m-gracia/esp32-bike-computer-main/docs/LCD_Round01.png

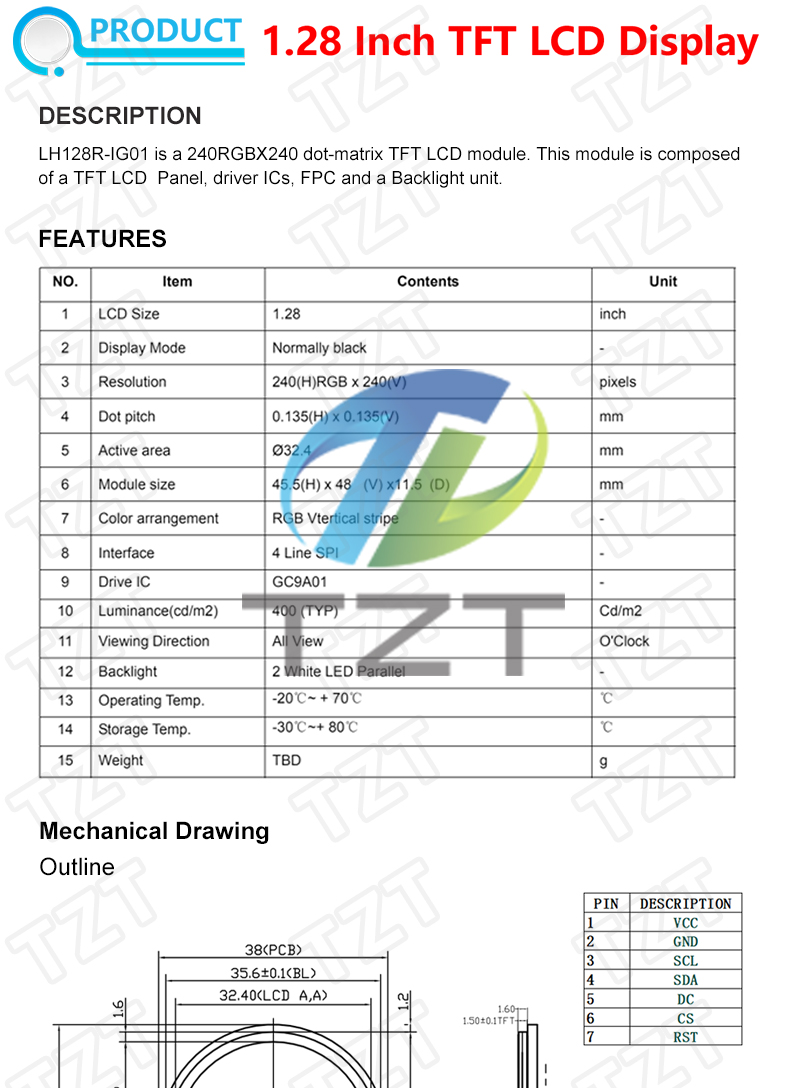
docs/LCD_Round01.png
