m-gracia/esp32-bike-computer-main/docs/LCD_Round02.png

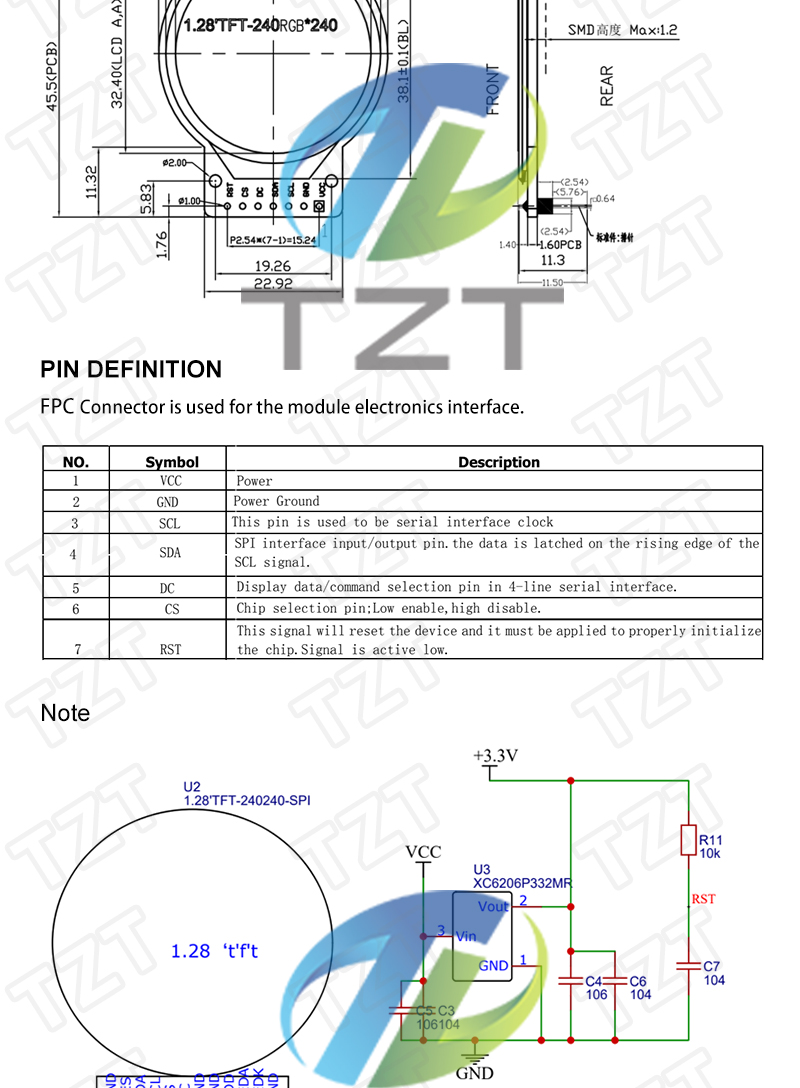
docs/LCD_Round02.png
