m-gracia/esp32-bike-computer-main/docs/OBD_ELM327_01.png

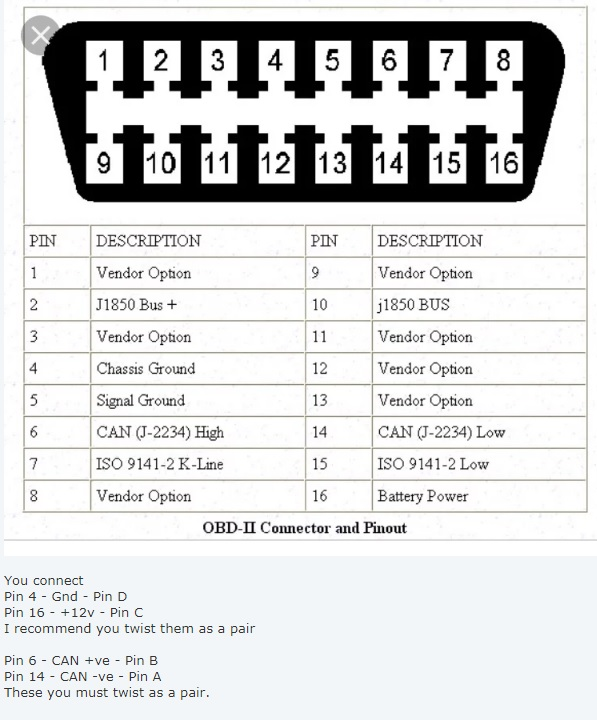
docs/OBD_ELM327_01.png
