m-gracia/esp32-bike-computer-main/docs/USB C.jpg

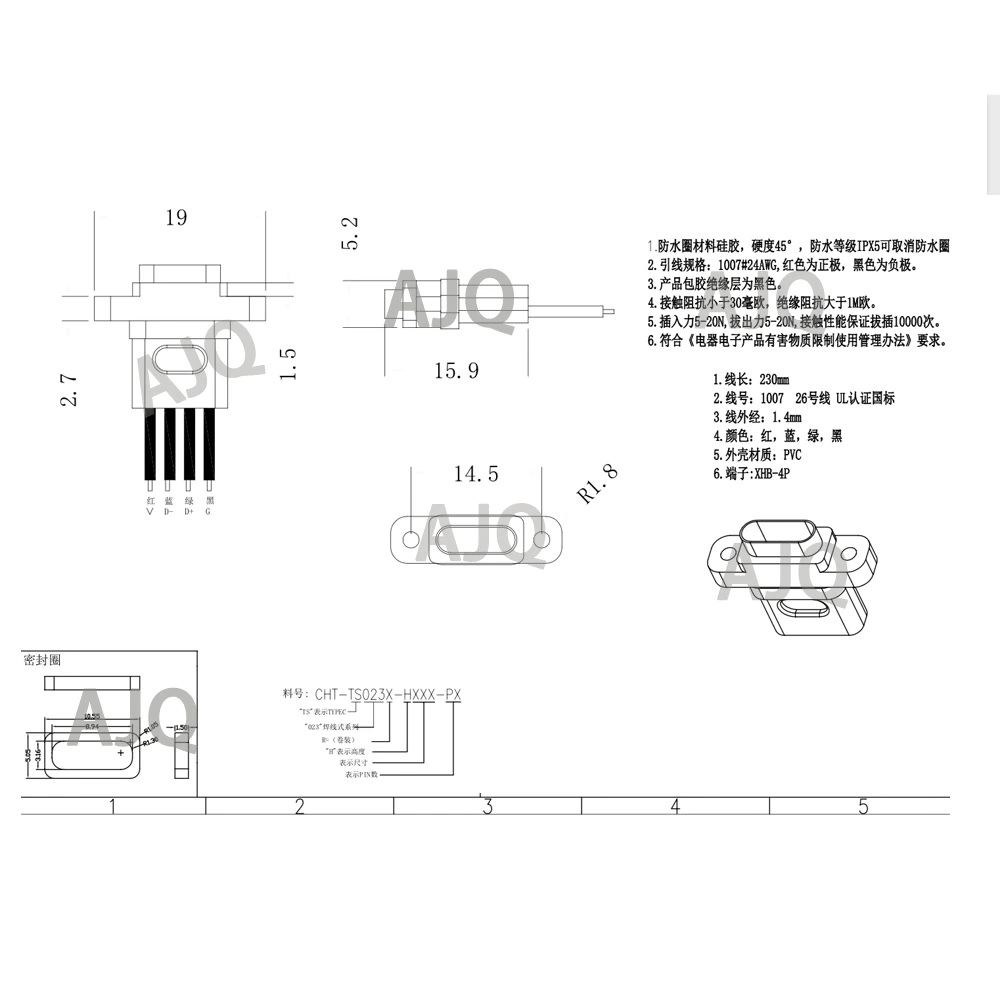
docs/USB C.jpg
