m-gracia/esp32-bike-computer-main/include/httpsrv.h

#ifndef _HTTPSRV_H_
#define _HTTPSRV_H_
#include <Arduino.h>

String webProcessor(const String& var); // Process webpages variables %VAR%
void initWeb();     // Initialize web server and OTA
void getWeb();      // Handle web server


// Style 
/*
static String style =
"<style>#file-input,input{width:100%;height:44px;border-radius:4px;margin:10px auto;font-size:15px}"
"input{background:#f1f1f1;border:0;padding:0 15px}body{background:#3498db;font-family:sans-serif;font-size:14px;color:#777}"
"#file-input{padding:0;border:1px solid #ddd;line-height:44px;text-align:left;display:block;cursor:pointer}"
"#bar,#prgbar{background-color:#f1f1f1;border-radius:10px}#bar{background-color:#3498db;width:0%;height:10px}"
"form{background:#fff;max-width:258px;margin:75px auto;padding:30px;border-radius:5px;text-align:center}"
".btn{background:#3498db;color:#fff;cursor:pointer}</style>";

// Login page
static String loginIndex = 
"<form name=loginForm>"
"<h1>ESP32 Login</h1>"
"<h5></h5>"
"<input name=userid placeholder='User ID'> "
"<input name=pwd placeholder=Password type=Password> "
"<input type=submit onclick=check(this.form) class=btn value=Login></form>"
"<script>"
"function check(form) {"
"if(form.userid.value=='admin' && form.pwd.value=='admin')"
"{window.open('/serverIndex')}"
"else"
"{alert('Error Password or Username')}"
"}"
"</script>" + style;
 
// Server Index Page
static String serverIndex = 
"<script src='/jquery.min.js'></script>"
"<form method='POST' action='#' enctype='multipart/form-data' id='upload_form'>"
"<input type='file' name='update' id='file' onchange='sub(this)' style=display:none>"
"<label id='file-input' for='file'>   Choose file...</label>"
"<input type='submit' class=btn value='Update'>"
"<br><br>"
"<div id='prg'></div>"
"<br><div id='prgbar'><div id='bar'></div></div><br></form>"
"<script>"
"function sub(obj){"
"var fileName = obj.value.split('\\\\');"
"document.getElementById('file-input').innerHTML = '   '+ fileName[fileName.length-1];"
"};"
"$('form').submit(function(e){"
"e.preventDefault();"
"var form = $('#upload_form')[0];"
"var data = new FormData(form);"
"$.ajax({"
"url: '/update',"
"type: 'POST',"
"data: data,"
"contentType: false,"
"processData:false,"
"xhr: function() {"
"var xhr = new window.XMLHttpRequest();"
"xhr.upload.addEventListener('progress', function(evt) {"
"if (evt.lengthComputable) {"
"var per = evt.loaded / evt.total;"
"$('#prg').html('progress: ' + Math.round(per*100) + '%');"
"$('#bar').css('width',Math.round(per*100) + '%');"
"}"
"}, false);"
"return xhr;"
"},"
"success:function(d, s) {"
"console.log('success!') "
"},"
"error: function (a, b, c) {"
"}"
"});"
"});"
"</script>" + style;

#define jquery_min_js_v3_2_1_gz_len 30178
PROGMEM const char jquery_min_js_v3_2_1_gz[]  = {
0x1f,0x8b,0x08,0x00,0x00,0x00,0x00,0x00,0x00,0x0a,0xcc,0xbd,0x69,0x77,0x1b,0x47,0x92,0x36,0xfa,0xfd,0xfd,0x15,0x44,0xb5,0x86,0x5d,0x25,0x24,0x41,0x50,0xb6,0xfb,0x9d,0x2e,0xa8,0x84,0x63,0x5b,0x56,0x5b,0x3d,0xde,0xda,0x92,0x97,0x1e,0x10,0xf6,0xa9,0x0d,0x40,0x81,0xd8,0x08,0x80,0xa2,0x64,0x02,0xf3,0xdb,0x6f,0x3c,0x11,0x99,0x59,0x59,0x0b,0x68,0xf7,0xcc,0x9d,0x73,0xaf,0x17,0xa2,0x96,0xac,0x5c,0x23,0x23,0x63,0x8f,0xcb,0xa7,0x9d,0xb3,0xf9,0x3f,0xee,0xf2,0xed,0x87,0xb3,0x77,0x1f,0xf5,0x9e,0xf5,0xae,0xce,0x0e,0x67,0x7e,0x1a,0x9c,0xfd,0xfd,0xcd,0xd9,0xab,0xf5,0xdd,0x2a,0x8b,0xf7,0xc5,0x7a,0x75,0x16,0xaf,0xb2,0xb3,0xf5,0x7e,0x96,0x6f,0xcf,0xd2,0xf5,0x6a,0xbf,0x2d,0x92,0xbb,0xfd,0x7a,0xbb,0xa3,0xa2,0xf3,0x5b,0x7c,0xda,0x5b,0x6f,0xa7,0x97,0x8b,0x22,0xcd,0x57,0xbb,0xfc,0xec,0xe9,0xe5,0xff,0xe9,0x4c,0xee,0x56,0x29,0x3e,0xf4,0x63,0x95,0x04,0x0f,0xde,0x1d,0x3d,0xde,0xd1,0x67,0xe9,0xde,0x1b,0x78,0xeb,0x64,0x9e,0xd3,0x45,0x14,0xed,0x3f,0x6c,0xf2,0xf5,0xe4,0x6c,0xb9,0xce,0xee,0x16,0xf9,0xf9,0xf9,0x89,0x17,0xbd,0xfc,0xfd,0x66,0xbd,0xdd,0xef,0x86,0xd5,0xdb,0x28,0xee,0x65,0xeb,0xf4,0x6e,0x99,0xaf,0xf6,0xc3,0x84,0x9a,0xe9,0xf4,0x83,0xb0,0x6c,0x35,0x78,0x28,0x26,0x7e,0xa7,0x2c,0x12,0xec,0x67,0xdb,0xf5,0xfd,0xd9,0x2a,0xbf,0x3f,0xfb,0x62,0xbb,0x5d,0x6f,0x7d,0x4f,0x8f,0x79,0x9b,0xdf,0xde,0x15,0xdb,0x7c,0x77,0x16,0x9f,0xdd,0x17,0xab,0x8c,0xca,0xdc,0x17,0xfb,0x19,0xdd,0x99,0x2f,0xbd,0x60,0xb0,0xcd,0xf7,0x77,0xdb,0xd5,0x19,0xb5,0x12,0x1c,0x43,0xfe,0xeb,0x7b,0x34,0x33,0xf9,0xa4,0x58,0xe5,0x99,0xd7,0x31,0xdd,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
